BramRausch/Microwth/Images and videos/Capture.PNG

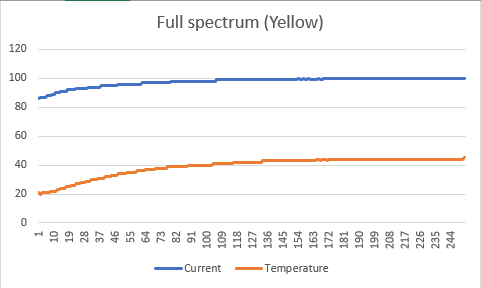
Images and videos/Capture.PNG
