BramRausch/Microwth/Images and videos/IMG_0162.JPG

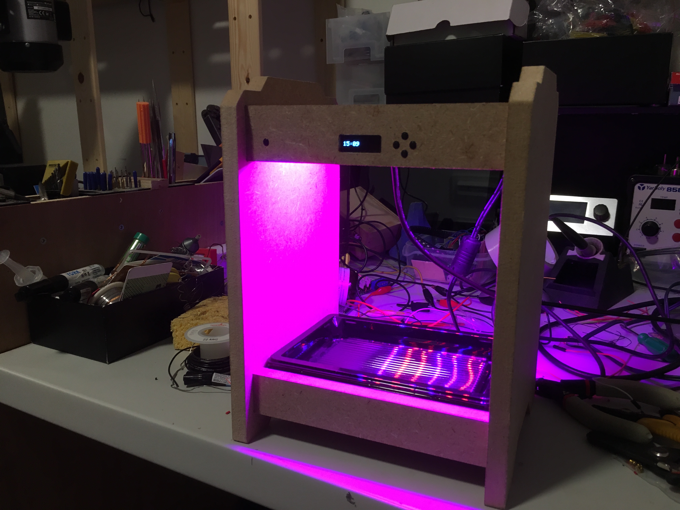
Images and videos/IMG_0162.JPG
