BramRausch/Microwth/Images and videos/IMG_0174.JPG

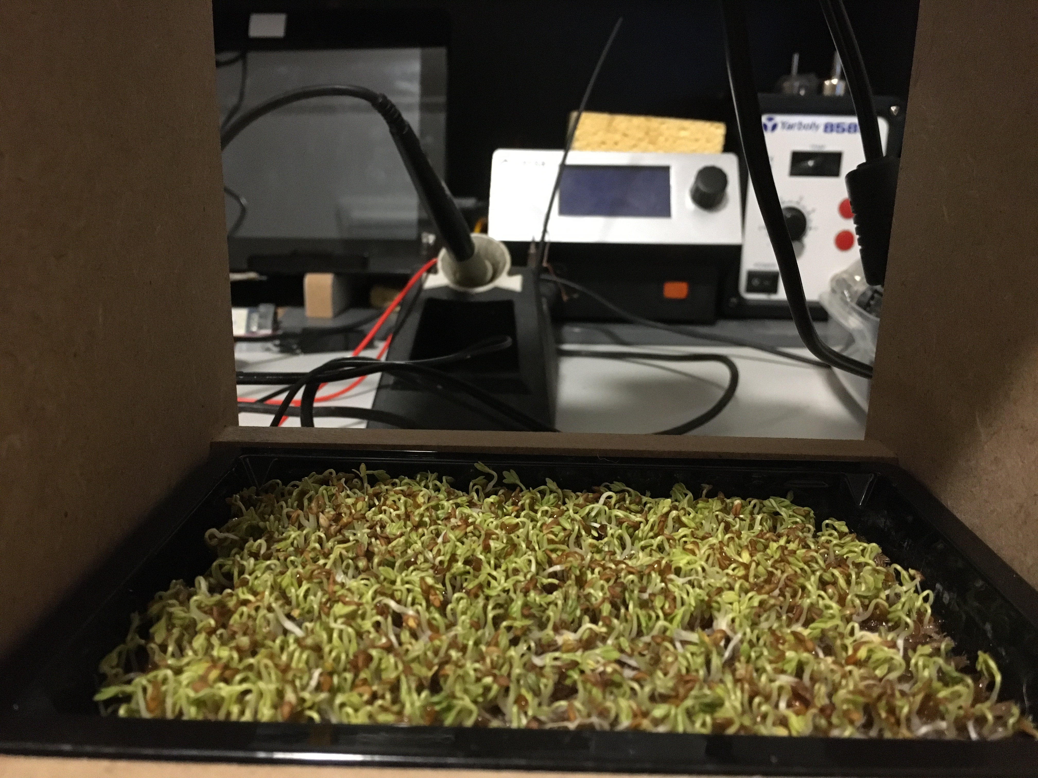
Images and videos/IMG_0174.JPG
