BramRausch/Microwth/Images and videos/IMG_0189.JPG

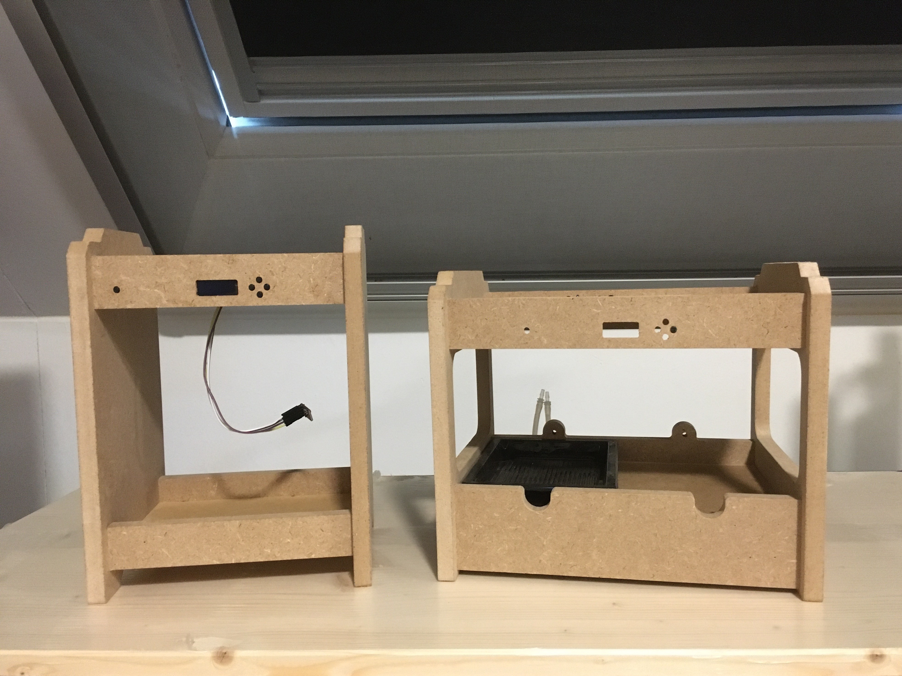
Images and videos/IMG_0189.JPG
