BramRausch/Microwth/Images and videos/IMG_0192.JPG

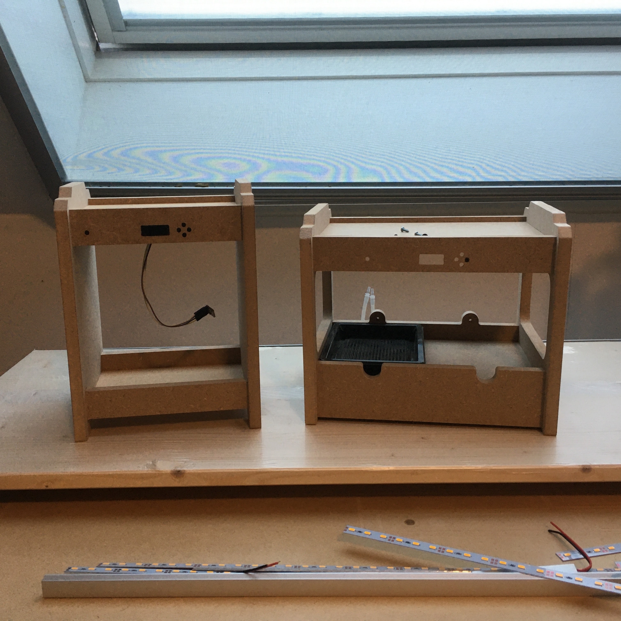
Images and videos/IMG_0192.JPG
