BramRausch/Microwth/Images and videos/IMG_0256.jpg

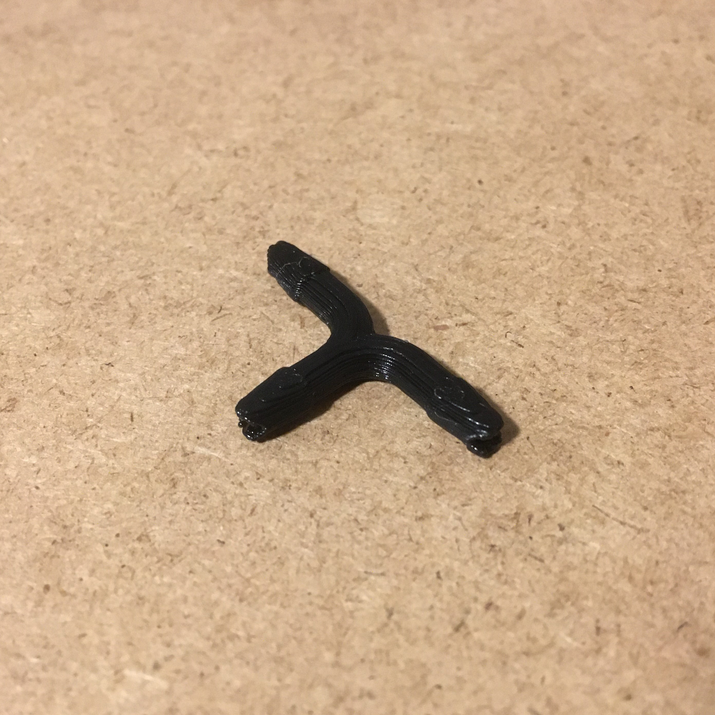
Images and videos/IMG_0256.jpg
