BramRausch/Microwth/Images and videos/IMG_0257.jpg

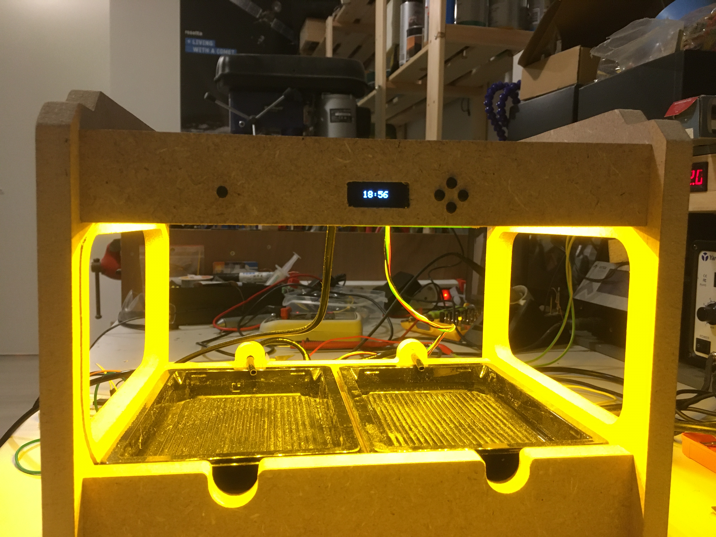
Images and videos/IMG_0257.jpg
