BramRausch/Microwth/Images and videos/IMG_0257_cropped.jpg

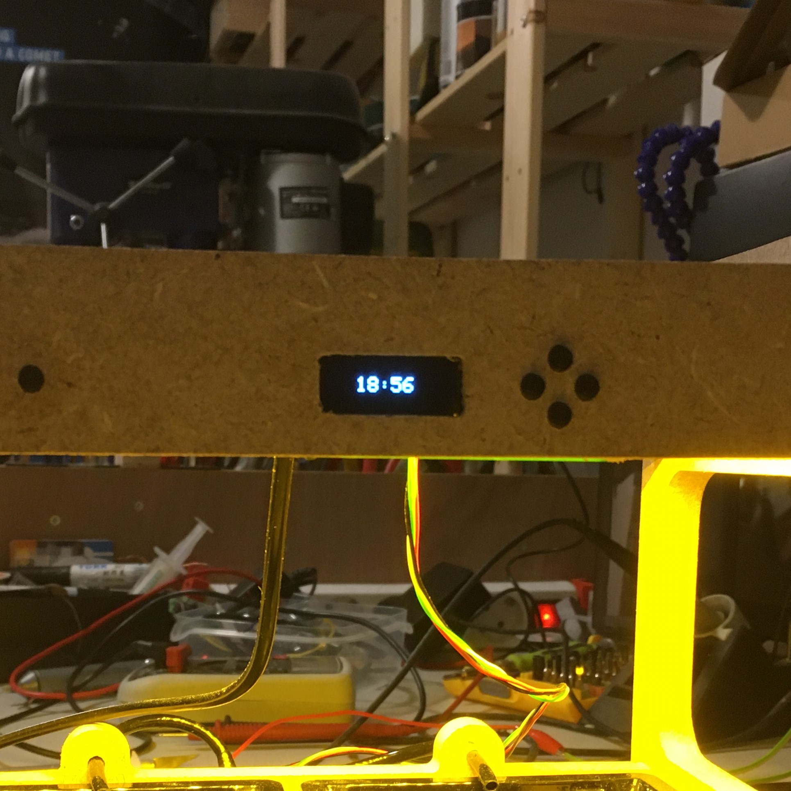
Images and videos/IMG_0257_cropped.jpg
