BramRausch/Microwth/Images and videos/IMG_0260.JPG

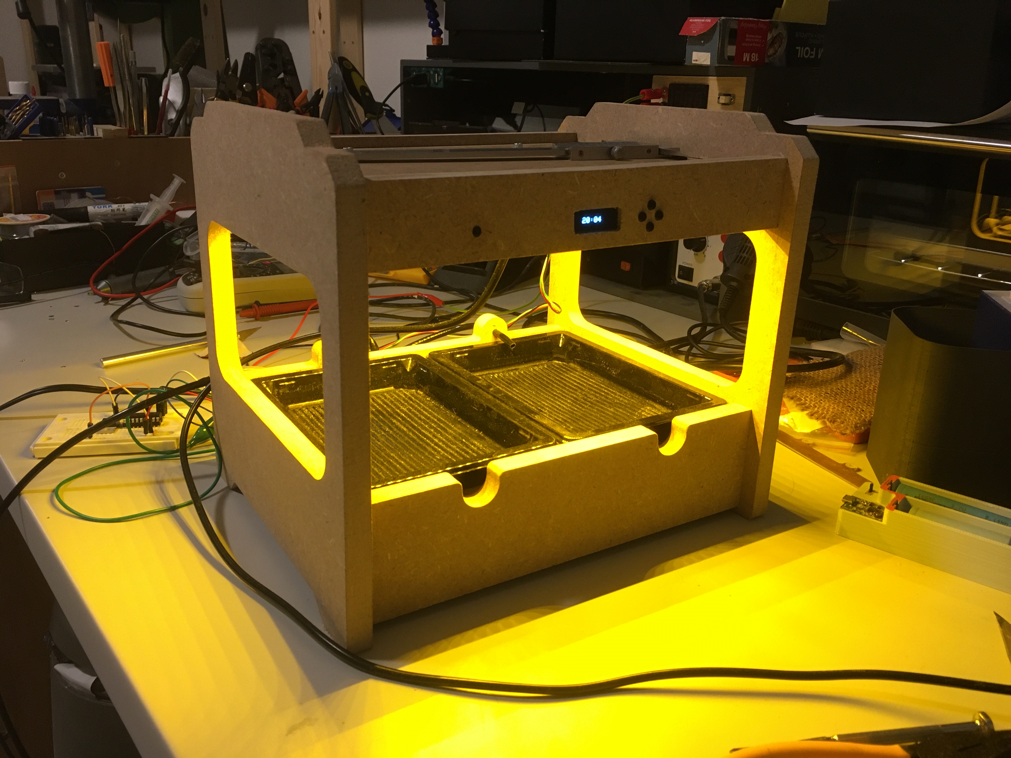
Images and videos/IMG_0260.JPG
