BramRausch/Microwth/Images and videos/IMG_0284.jpg

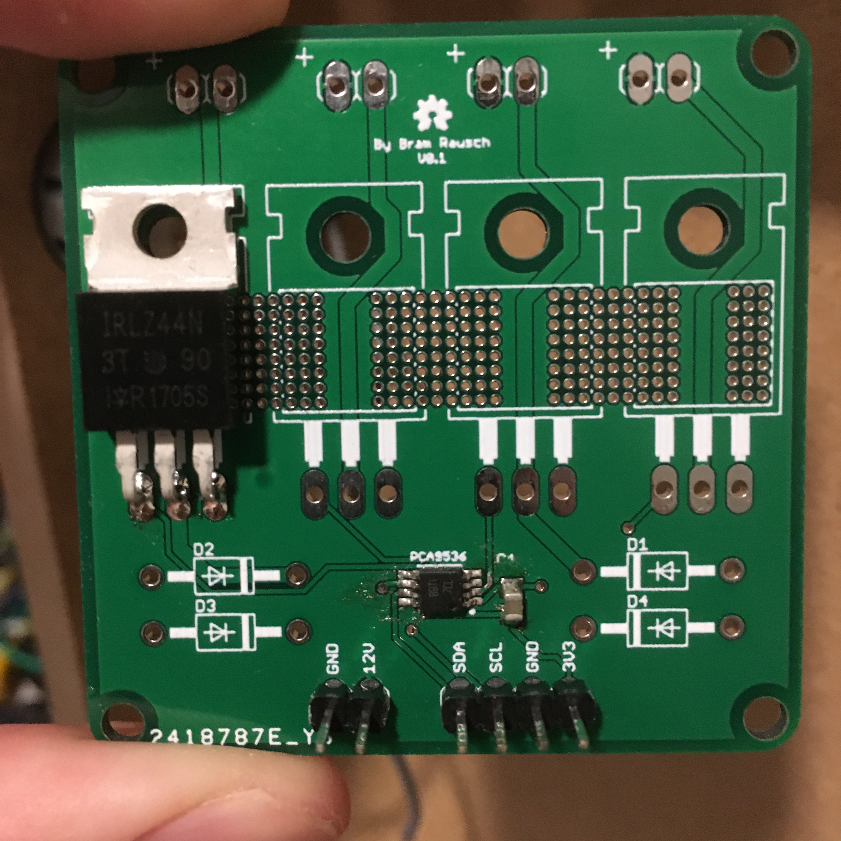
Images and videos/IMG_0284.jpg
