BramRausch/Microwth/Images and videos/IMG_0287.jpg

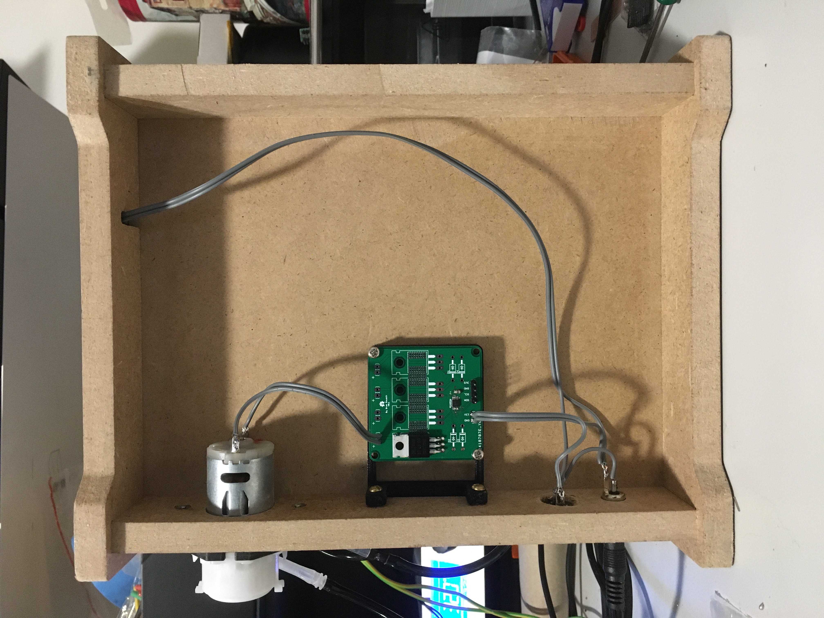
Images and videos/IMG_0287.jpg
