BramRausch/Microwth/Images and videos/Microwth_-_1x2_-_12mm_2019-Nov-04_10-16-37PM-000_CustomizedView4593919631.png

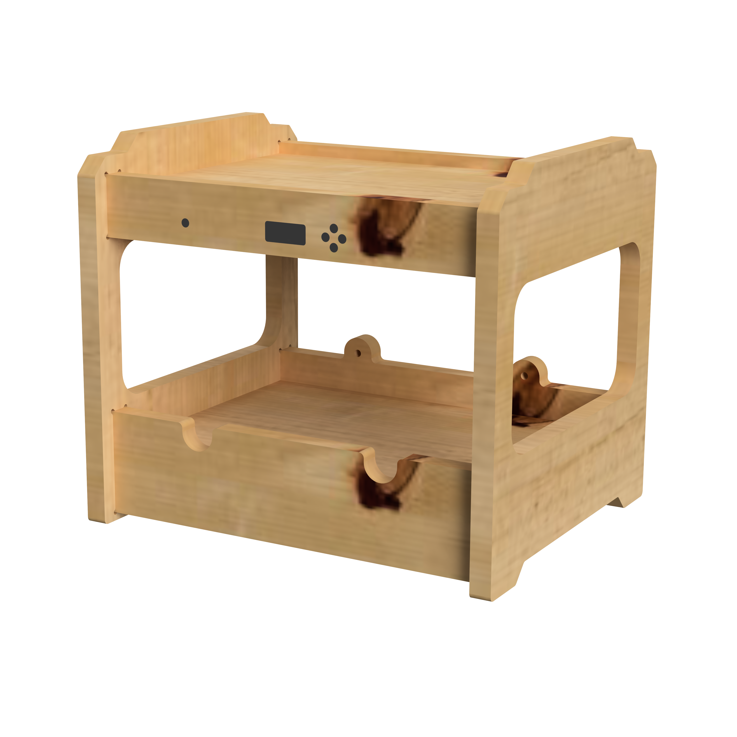
Images and videos/Microwth_-_1x2_-_12mm_2019-Nov-04_10-16-37PM-000_CustomizedView4593919631.png
