BramRausch/Microwth/Images and videos/IMG_0160.JPG

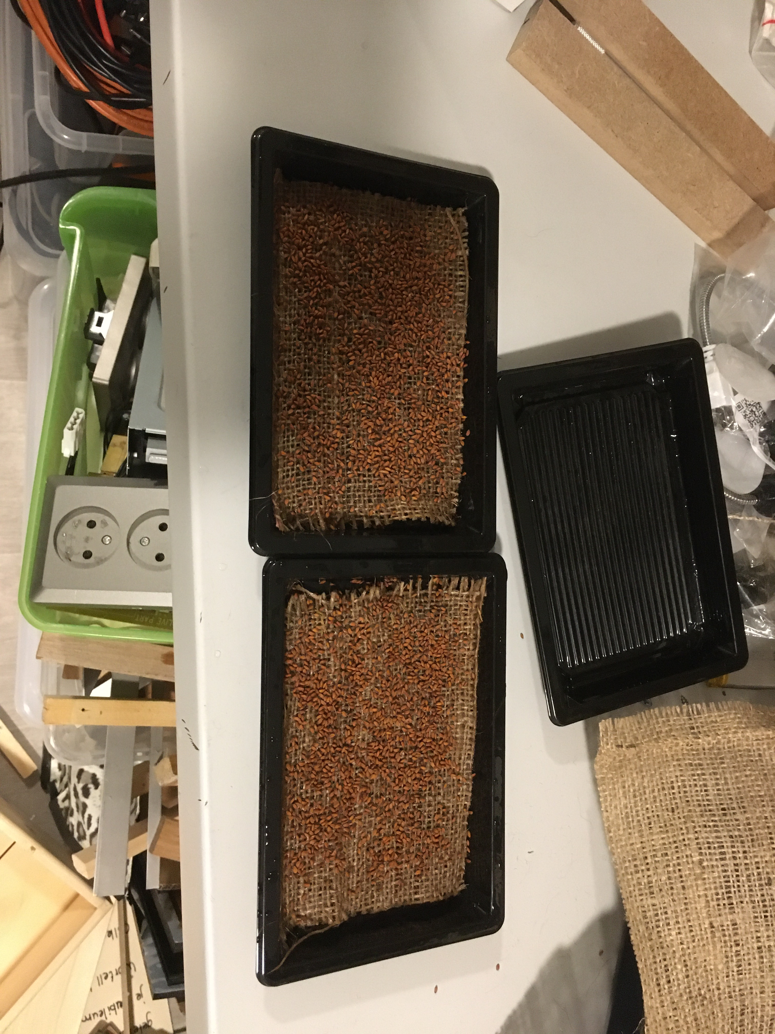
Images and videos/IMG_0160.JPG
